laukik-hase/Li-Fi/Circuits/Analysis - 2.jpg

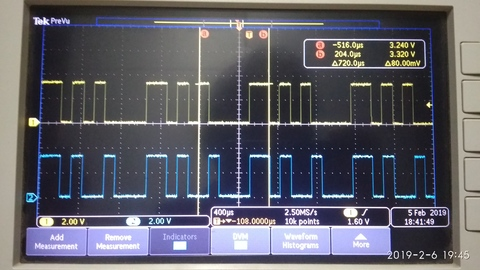
Circuits/Analysis - 2.jpg
