laukik-hase/Li-Fi/Circuits/Analysis - 3.jpg

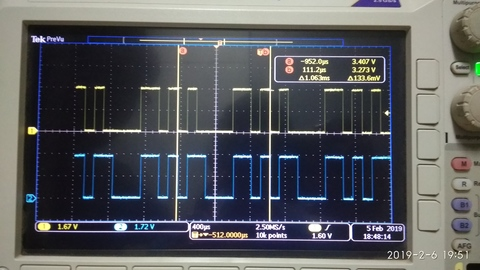
Circuits/Analysis - 3.jpg
