laukik-hase/Li-Fi/Circuits/Comparator.jpg

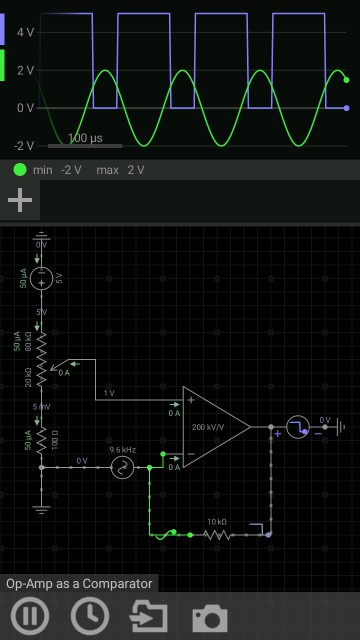
Circuits/Comparator.jpg
