laukik-hase/Li-Fi/Circuits/Comparator.png

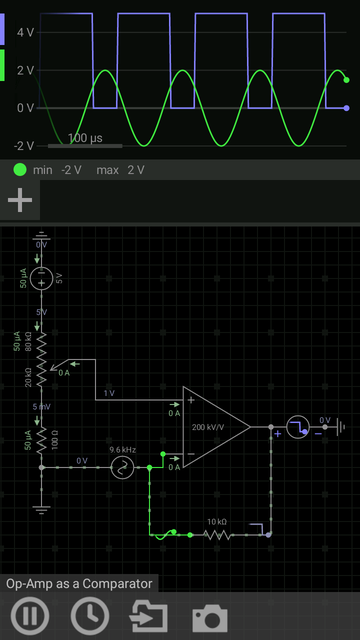
Circuits/Comparator.png
