laukik-hase/Li-Fi/Circuits/HS Transimpedance Amplifier.png

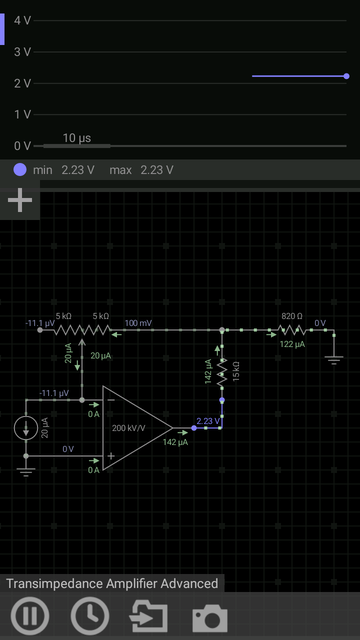
Circuits/HS Transimpedance Amplifier.png
