laukik-hase/Li-Fi/Circuits/Schmitt Trigger (Hysteresis).png

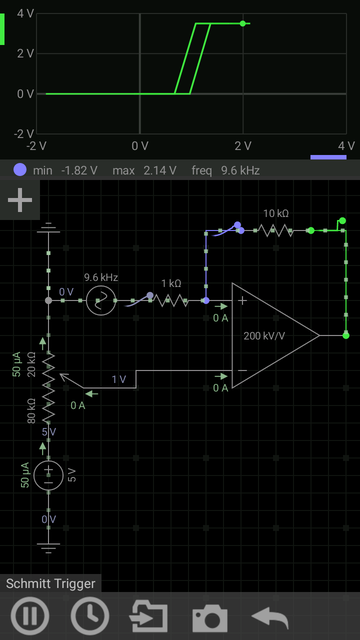
Circuits/Schmitt Trigger (Hysteresis).png
