laukik-hase/Li-Fi/Circuits/Waveform Deprecation - 1.jpg

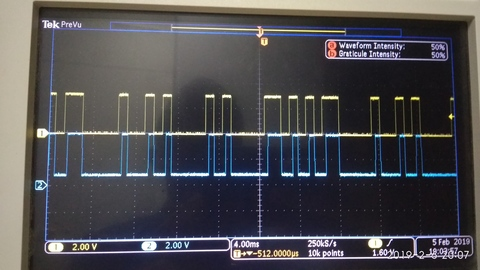
Circuits/Waveform Deprecation - 1.jpg
