laukik-hase/Li-Fi/Circuits/Waveform Deprecation - 2.jpg

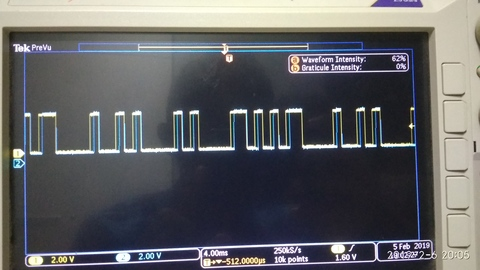
Circuits/Waveform Deprecation - 2.jpg
