laukik-hase/Li-Fi/Circuits/lifi_hardware_setup.jpeg

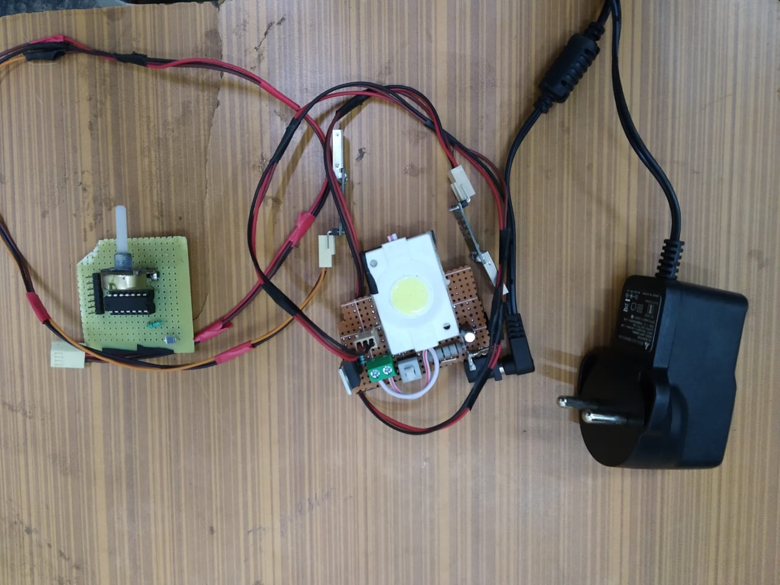
Circuits/lifi_hardware_setup.jpeg
