laukik-hase/Li-Fi/Codes/gui_python/rec_gui.py

import easygui
import base64
import serial
ser = serial.Serial("/dev/ttyUSB1",2000000,timeout=0)
y=""
while 1:
	if ser.inWaiting():
		x= ser.read()
		if x is "~":
			break
		y+=x
		print(x)
		x=""
filename = easygui.filesavebox()	
file = open(filename,"wb")
file.write(y.decode('base64'))
file.close()
ser.close()
