laukik-hase/Li-Fi/Codes/gui_python/trans_gui.py

import easygui
import base64
import serial
ser = serial.Serial("/dev/ttyUSB0",2000000,timeout=0)
filename = easygui.fileopenbox()
with open(filename,"rb") as imgfile:
	str1 = base64.b64encode(imgfile.read())
	ser.write(str1)
	print(str1)
	ser.write("~")

ser.close()
